hmaerki/octohub/octohub_kicad_v0.2/commissioning/README_try_v0.1b/20240614-0003.png

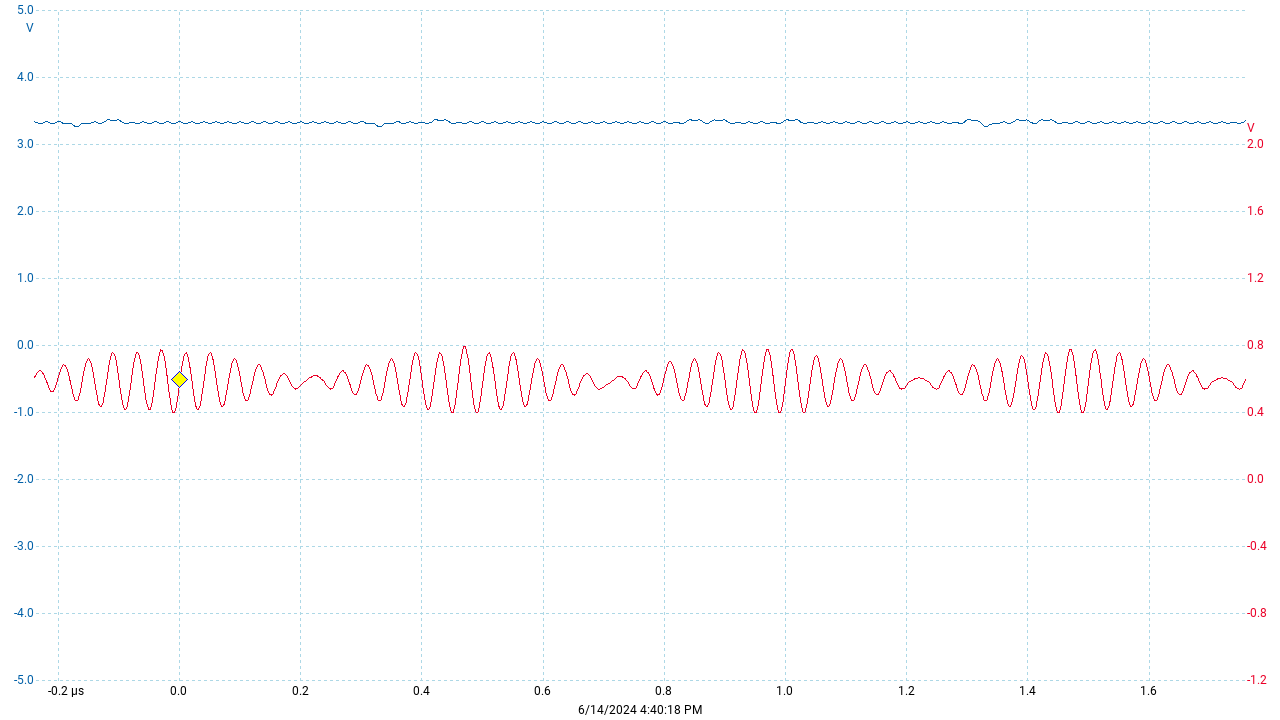
octohub_kicad_v0.2/commissioning/README_try_v0.1b/20240614-0003.png
